christian-kramer/USB-Throttle-Quadrant/Mechanical/Test Parts/Bearing Outer.stl

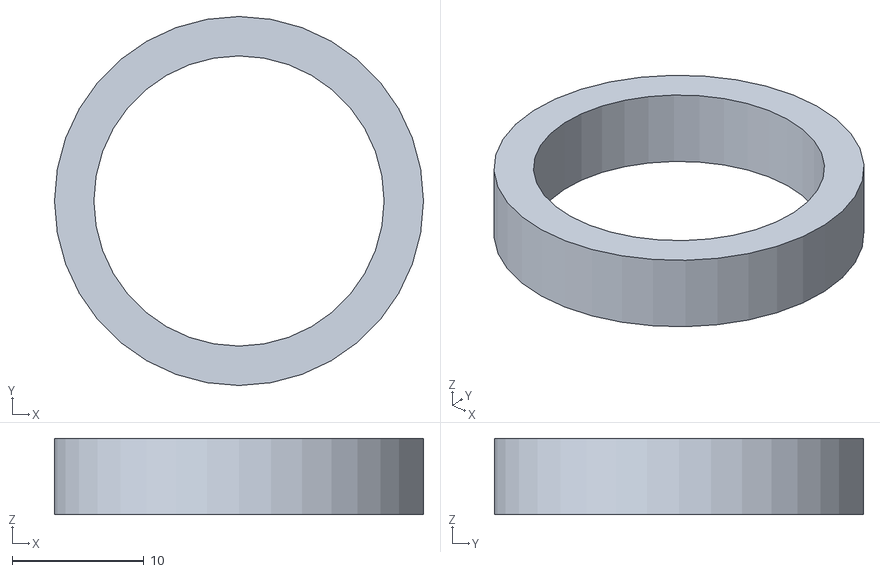
[picture p15: CAD file, 2020-07-15]
Mechanical/Test Parts/Bearing Outer.stl
28.0 x 28.0 x 5.80
